Bbagley24/ECEN_403_Team54/Documents and Reports/Semester 1 (ECEN 403)/Progress Reports/Progress Reprot 10_14.docx

Erica:

- Completed layout for website + enhanced design + functionality
- Currently working on setting up RTMP for video streaming to website

Julia:

- Completed Subsystem Intro Project
- Completed buck converter designs and simulations (all in WEBENCH)
  - Steady state simulations
  - Load transient simulations
  - Input transient simulations
- Found surface mount connectors compatible with power source
- Found pwm ic
  - TS5A4597DBVR
- Currently designing overall circuit in altium
  - Might need to create parts for the connector

Blake:

- Both Intro Projects are finished

Next:

- Switch-State Determination
- Training Data
- Start on image recognition
