Bbagley24/ECEN_403_Team54/Documents and Reports/Semester 1 (ECEN 403)/Progress Reports/Project Update 10_9.docx

Erica:

- Made search functionality properly working
- Redid some of the website layout to look sleeker
- Put in blank videos as placeholders
- Next Steps (already started):
  - Setup RTMP (real-time messaging protocol) server and HLS (HTTP Live Streaming) for live stream video

Blake:

- Microcontroller Intro Project complete
- About halfway through ML Intro Project
- Next Steps :
  - Finish ML Intro Project
  - Make training data
  - Start on Image Recognition

Julia:

- 75% done with intro project
- Buck Converters designed and simulated
  - Need to find pwm chips (will do thursday)
- Next Steps:
  - Order parts for converters that need to be ordered
  - Begin pcb design for the actual project (hope to be close to finished on monday)
