Bbagley24/ECEN_403_Team54/Documents and Reports/Semester 1 (ECEN 403)/Progress Reports/Project Update 11_11.docx

Erica:

- Completely finished drag/drop map, fixed issues throughout website
- Website is in finished state for demo
- Currently working:
  - Adding small features + improve look/design
  - Final Presentation/ Report

Julia:

- Finished soldering the board
- currently
  - testing the buck converters with the oscilloscope

Blake:

- Synching camera is near perfect
- Memory size problem fixed
- Image processing has been started (mainly waiting on image data to fine tune values)
- Currently working
  - Fix remaining memory problems
  - Finishing image processing
  - Finishing camera output accuracy
  - Combining features together in one flash
