Bbagley24/ECEN_403_Team54/Presentations/Semester 1 (ECEN 403)/Blake Demo Slides.pptx

## Blake Bagley Demo


## Microcontroller (Blake)

Receiving Camera Data
- Each segment has 60 packets with a packet ID from 0-59
- Each segment has a segment ID on 20th packet from 1-4

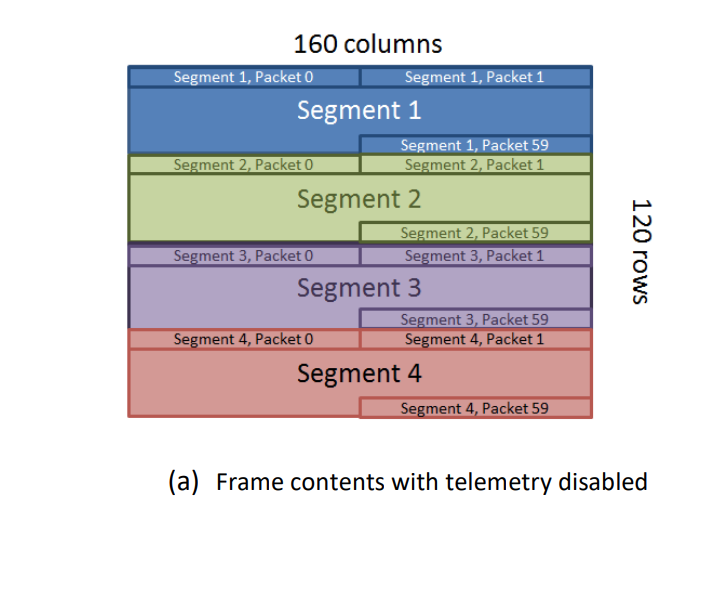
[picture p34: figure]

Figure taken from FLiR Lepton Datasheet

## Microcontroller (Blake)

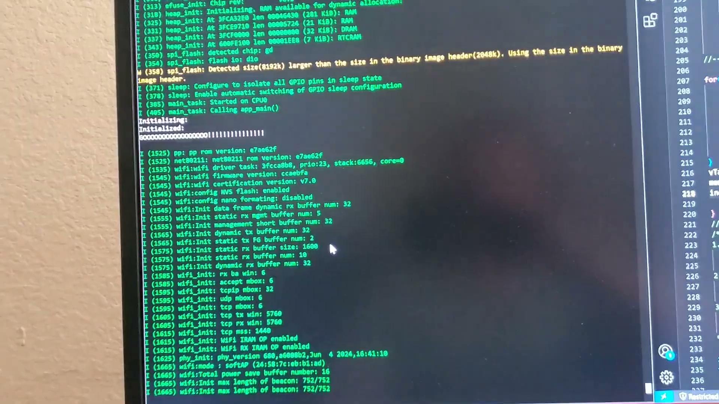
[picture p35: figure]

## Microcontroller (Blake)

Image Processing
- I first normalize the pixel data to an 8-bit mapping (0-255)
- Calculate the difference between the average heat of the frame and the designated window

Nothing in frame

Heat in bottom half

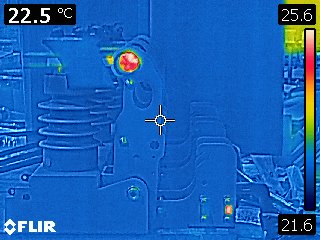
[picture p36: figure]

Heat in top half

Heat in left half

Heat in right half
